Interaktive-Medien/apibox/mc/lautstaerke.h

/******************************************************************************
 *  lautstaerke.h
 *  INMP441 I2S MEMS-Mikrofon — Lautstaerke in dB
 *  Keine Drittanbieter-Library (ESP-IDF I2S-Treiber).
 *
 *  Anschluss:
 *  INMP441: VDD  <->  ESP32-C6: 3.3V
 *  INMP441: GND  <->  ESP32-C6: GND
 *  INMP441: SD   <->  ESP32-C6: GPIO13
 *  INMP441: SCK  <->  ESP32-C6: GPIO2
 *  INMP441: WS   <->  ESP32-C6: GPIO23
 *  INMP441: L/R  <->  ESP32-C6: GND
 *
 *  Kalibration: Der dB-Shift-Faktor wird persistent in Preferences gespeichert
 *  (Namespace "calib", Key "kf_lautst" — NVS-Keys max. 15 Zeichen, daher Kurzform
 *  der Variable "kalibrationsfaktor_lautstaerke"). Default 122.0.
 *  Ermittlung einmalig mit calibration/lautstaerke_kalibrieren.ino
 *  (Vergleich gegen ein Smartphone-dB-Messgeraet).
 *****************************************************************************/

#ifndef LAUTSTAERKE_H
#define LAUTSTAERKE_H

#include <driver/i2s.h>
#include <math.h>

#define I2S_WS 23
#define I2S_SD 13
#define I2S_SCK 2
#define I2S_PORT I2S_NUM_0

#define SAMPLE_RATE 16000
#define BITS_PER_SAMPLE I2S_BITS_PER_SAMPLE_32BIT

const int DMA_BUF_COUNT = 8;
const int DMA_BUF_LEN = 1024;
const int BUFFER_SIZE = 512;
int32_t samples[BUFFER_SIZE];

// Variable für den Offset (wird im setup() aus dem Speicher überschrieben)
float mic_db_offset = 120.0;

// aufgerufen in mc.ino
void setupLautstaerke()
{
  // 1. Gespeicherten Offset abrufen
  preferences.begin("sensorbox", true); // true = reiner Lesezugriff
  // Lese "dboffset". Falls er nicht existiert, verwende 120.0 als Fallback
  mic_db_offset = preferences.getFloat("dboffset", 120.0);
  preferences.end();

  // 2. I2S Mikrofon initialisieren
  i2s_config_t i2s_config = {
      .mode = (i2s_mode_t)(I2S_MODE_MASTER | I2S_MODE_RX),
      .sample_rate = SAMPLE_RATE,
      .bits_per_sample = BITS_PER_SAMPLE,
      .channel_format = I2S_CHANNEL_FMT_ONLY_LEFT,
      .communication_format = I2S_COMM_FORMAT_STAND_I2S,
      .intr_alloc_flags = ESP_INTR_FLAG_LEVEL1,
      .dma_buf_count = DMA_BUF_COUNT,
      .dma_buf_len = DMA_BUF_LEN,
      .use_apll = false};

  i2s_pin_config_t pin_config = {
      .mck_io_num = I2S_PIN_NO_CHANGE,
      .bck_io_num = I2S_SCK,
      .ws_io_num = I2S_WS,
      .data_out_num = I2S_PIN_NO_CHANGE,
      .data_in_num = I2S_SD};

  if (i2s_driver_install(I2S_PORT, &i2s_config, 0, NULL) != ESP_OK)
  {
    Serial.println("I2S Installation fehlgeschlagen!");
    return;
  }
  i2s_set_pin(I2S_PORT, &pin_config);
  i2s_zero_dma_buffer(I2S_PORT);

  Serial.println("Mikrofon bereit.");
}

// aufgerufen in mc.ino
float getLautstaerke()
{
  size_t bytesRead = 0;

  // 1. Alte DMA-Puffer leeren (verhindert das Lesen von veralteten Werten aus den letzten 15s)
  while (true)
  {
    i2s_read(I2S_PORT, &samples, sizeof(samples), &bytesRead, 0);
    if (bytesRead == 0) break;
  }

  // 2. Frische Puffer einlesen (ca. 100ms) für einen stabilen Momentanwert
  float sumSPL = 0;
  int validReads = 0;

  for (int b = 0; b < 4; b++)
  {
    esp_err_t result = i2s_read(I2S_PORT, &samples, sizeof(samples), &bytesRead, portMAX_DELAY);
    if (result == ESP_OK && bytesRead > 0)
    {
      int samplesCount = bytesRead / 4;
      float sumSq = 0;
      for (int i = 0; i < samplesCount; i++)
      {
        int32_t val = samples[i] >> 8;
        float floatSample = (float)val / 8388608.0;
        sumSq += (floatSample * floatSample);
      }
      float rms = sqrt(sumSq / samplesCount);
      float db = 20.0 * log10(rms + 1e-9);

      // Hier wird nun der geladene mic_db_offset addiert
      float spl = db + mic_db_offset;
      sumSPL += spl;
      validReads++;
    }
  }

  if (validReads > 0)
  {
    return sumSPL / validReads;
  }
  
  return 0.0;
}

#endif
